wesley-cantarino/Ultrasonic_Sensor_With_arduino/codeIOT_2018/application.windows/data/main_photo.png

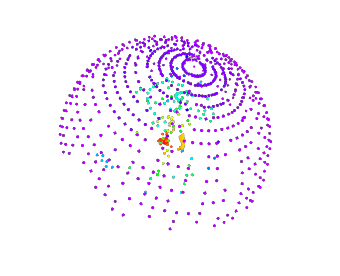
codeIOT_2018/application.windows/data/main_photo.png
